CodeCopyer996/PProbot/3.Model/lianzhouqi.SLDPRT

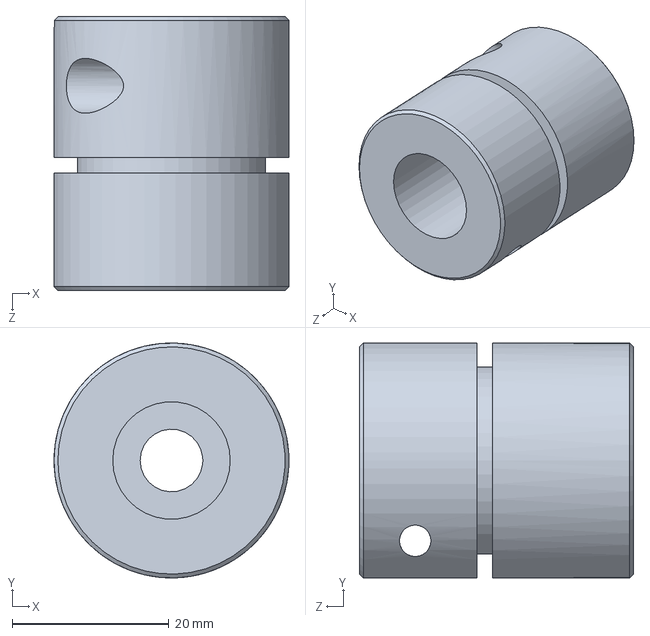
[picture p57: CAD file, 2023-08-03]
3.Model/lianzhouqi.SLDPRT
30.0 x 30.0 x 35.0 mm
