CodeCopyer996/PProbot/3.Model/大臂电机支架.SLDPRT

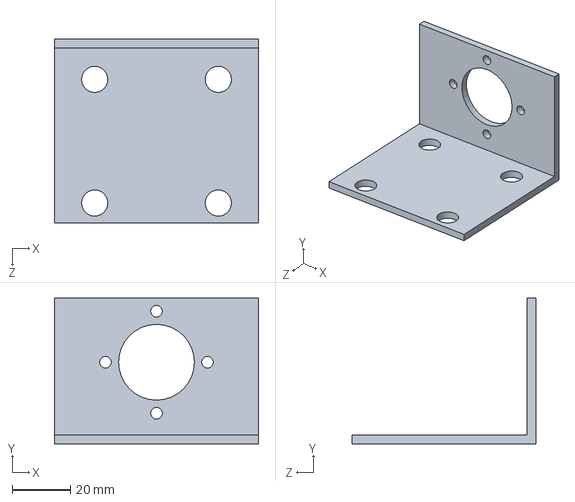
[picture p58: CAD file, 2023-08-03]
3.Model/大臂电机支架.SLDPRT
70.0 x 50.0 x 63.0 mm
