CodeCopyer996/PProbot/3.Model/6902带挡边轴承.SLDPRT

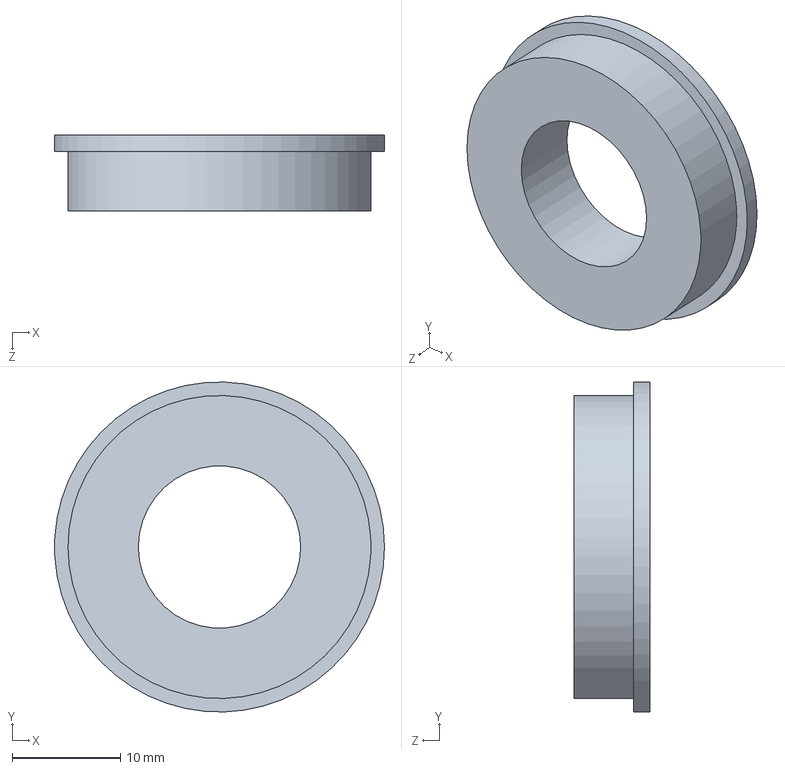
[picture p59: CAD file, 2023-08-03]
3.Model/6902带挡边轴承.SLDPRT
30.5 x 30.5 x 7.00 mm
