CodeCopyer996/PProbot/3.Model/27：1双轴减速器.SLDPRT

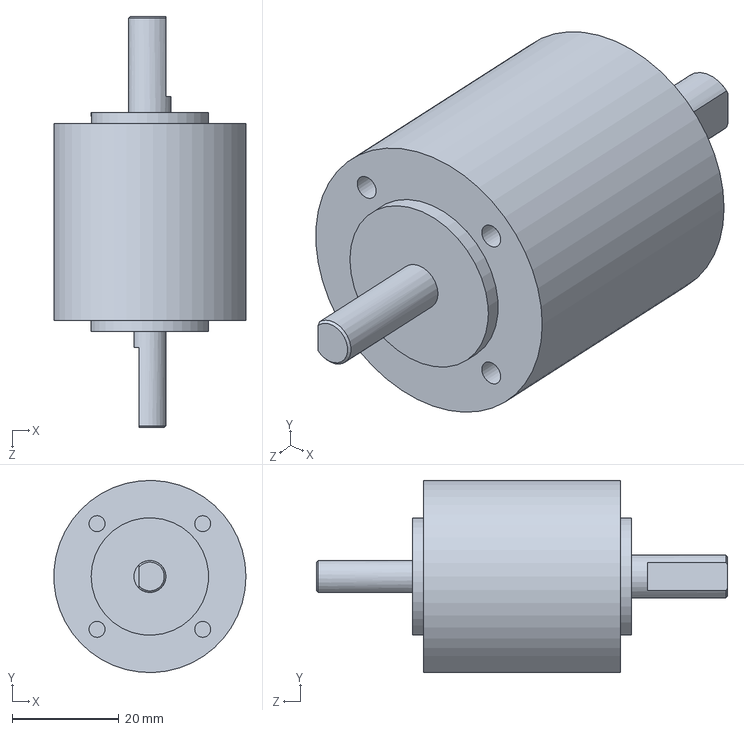
[picture p60: CAD file, 2023-08-03]
3.Model/27：1双轴减速器.SLDPRT
36.0 x 36.0 x 77.0 mm
