CodeCopyer996/PProbot/3.Model/小臂右1.SLDPRT

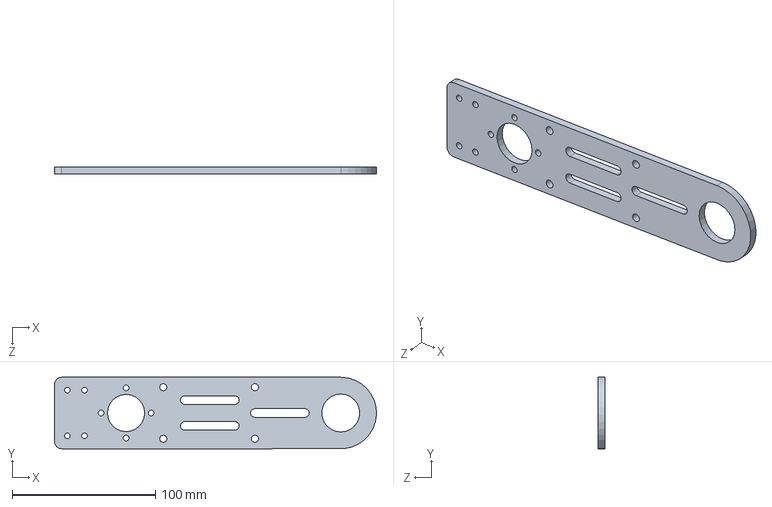
[picture p61: CAD file, 2023-08-03]
3.Model/小臂右1.SLDPRT
225.0 x 50.0 x 5.00 mm
