CodeCopyer996/PProbot/3.Model/皮带10-11.SLDPRT

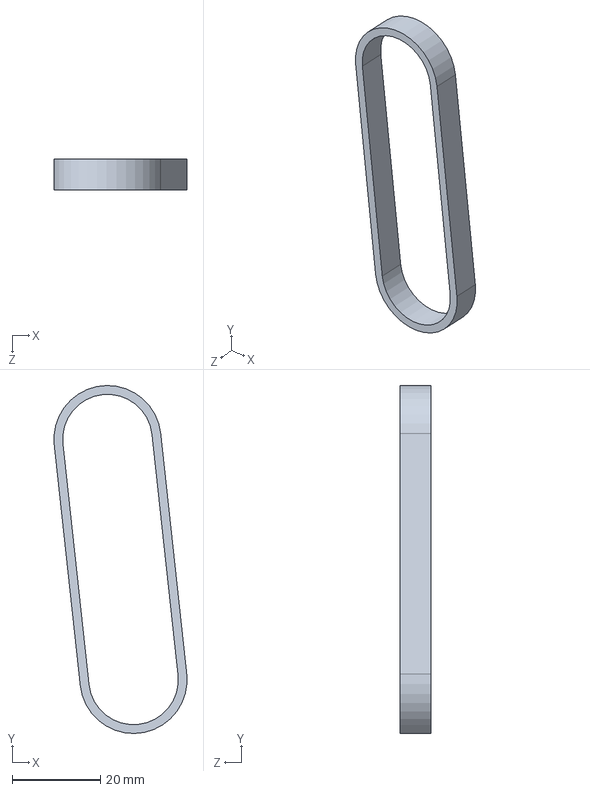
[picture p62: CAD file, 2023-08-03]
3.Model/皮带10-11.SLDPRT
30.1 x 78.8 x 7.00 mm
