CodeCopyer996/PProbot/3.Model/减速器固定.SLDPRT

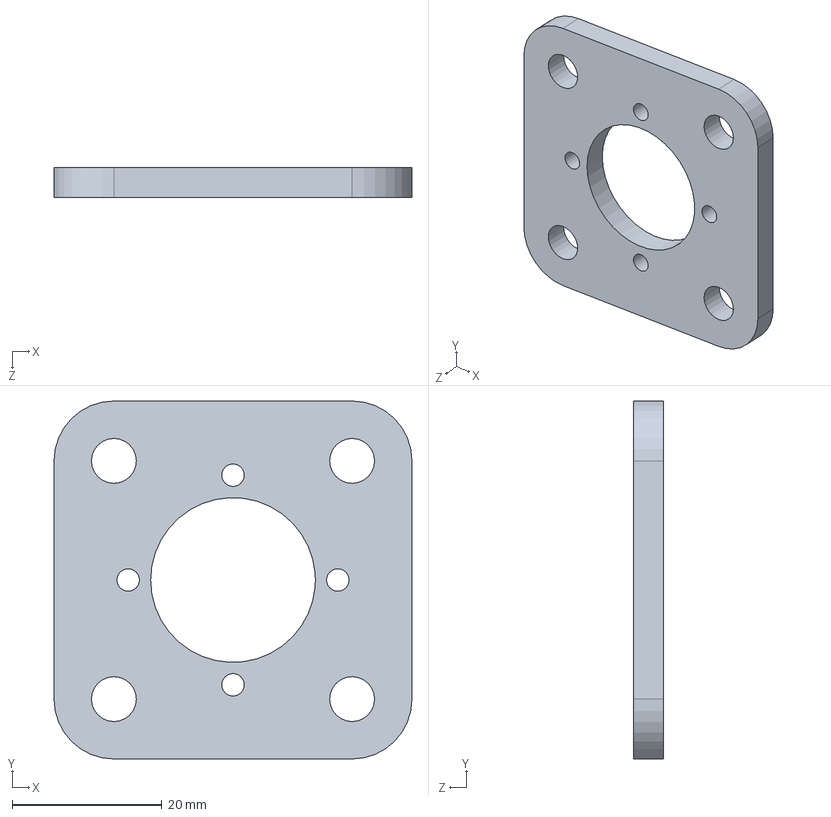
[picture p63: CAD file, 2023-08-03]
3.Model/减速器固定.SLDPRT
47.8 x 47.8 x 4.00 mm
