CodeCopyer996/PProbot/3.Model/小臂中.SLDPRT

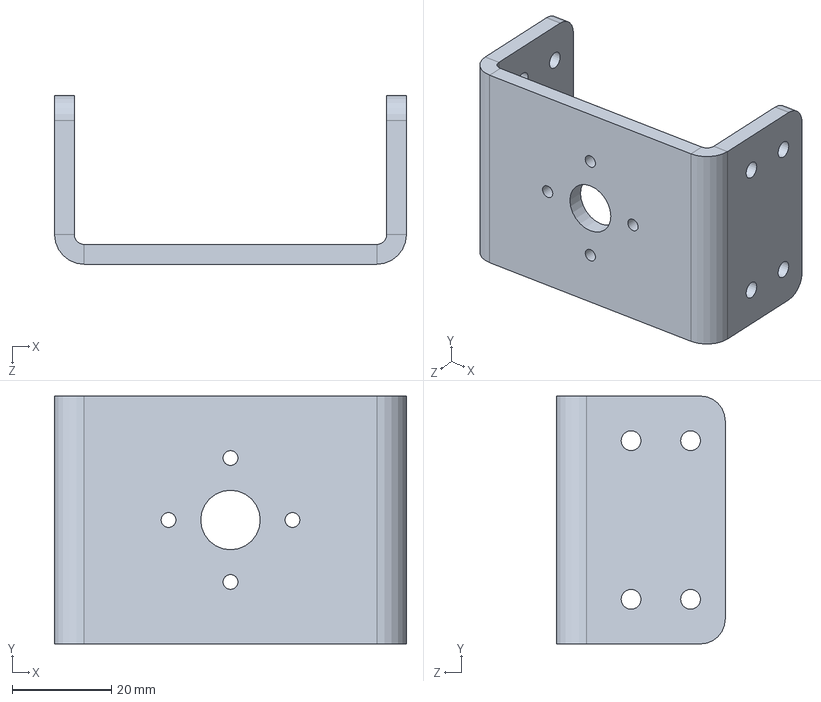
[picture p64: CAD file, 2023-08-03]
3.Model/小臂中.SLDPRT
71.0 x 50.0 x 34.0 mm
