CodeCopyer996/PProbot/3.Model/旋转轴6.SLDPRT

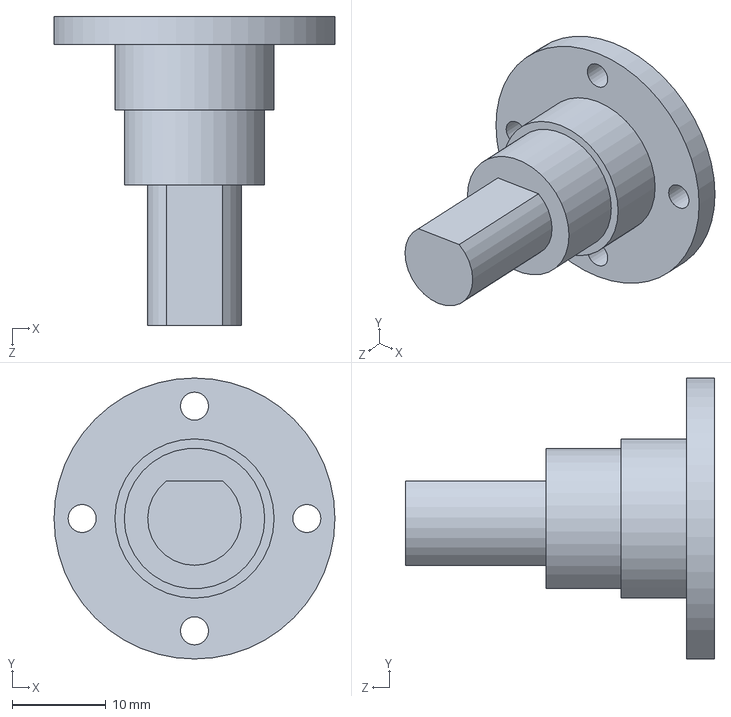
[picture p65: CAD file, 2023-08-03]
3.Model/旋转轴6.SLDPRT
30.0 x 30.0 x 33.0 mm
