CodeCopyer996/PProbot/3.Model/底座支撑.SLDPRT

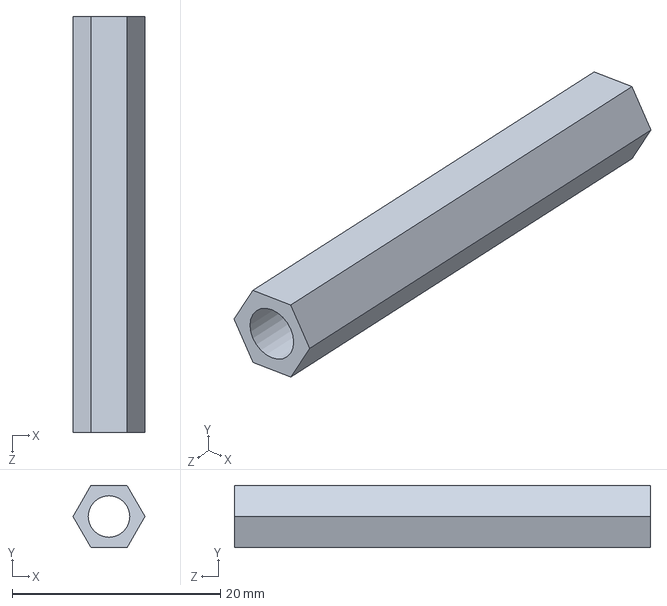
[picture p66: CAD file, 2023-08-03]
3.Model/底座支撑.SLDPRT
6.93 x 6.01 x 40.0 mm
