CodeCopyer996/PProbot/3.Model/大臂.SLDPRT

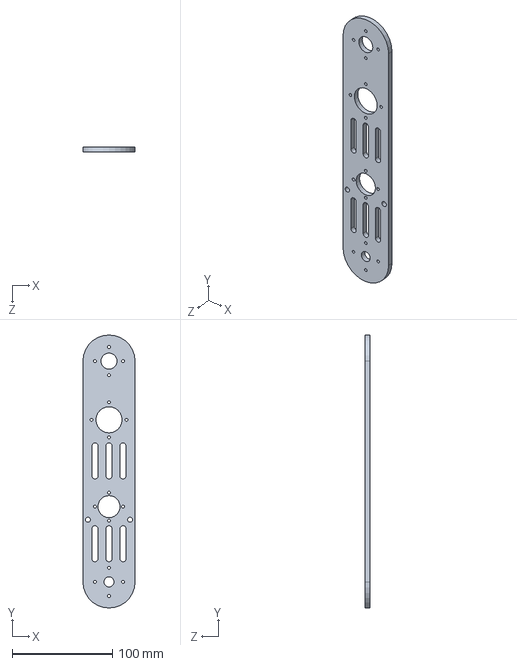
[picture p67: CAD file, 2023-08-03]
3.Model/大臂.SLDPRT
52.0 x 272.0 x 5.00 mm
