CodeCopyer996/PProbot/3.Model/云台旋转板.SLDPRT

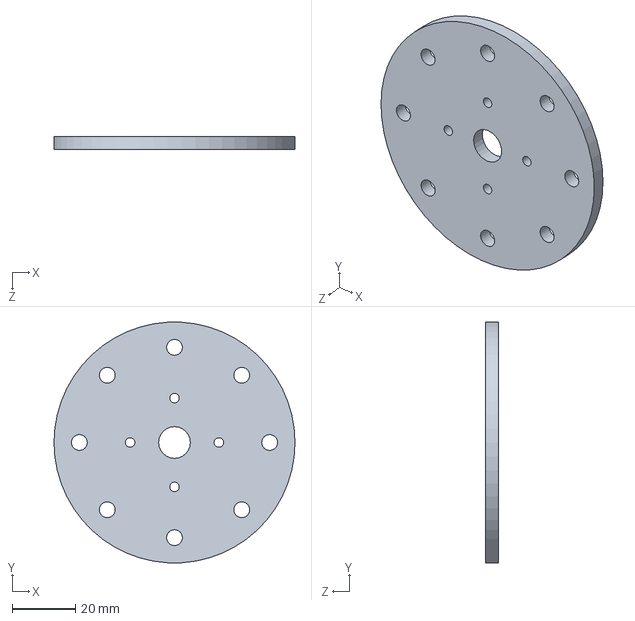
[picture p68: CAD file, 2023-08-03]
3.Model/云台旋转板.SLDPRT
76.0 x 75.9 x 4.00 mm
