CodeCopyer996/PProbot/3.Model/小臂p1.SLDPRT

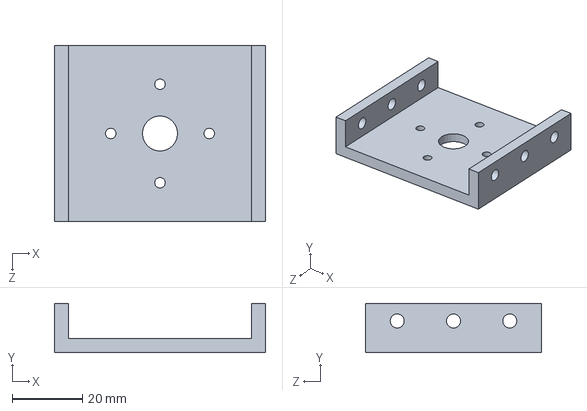
[picture p69: CAD file, 2023-08-03]
3.Model/小臂p1.SLDPRT
60.0 x 14.0 x 50.0 mm
