CodeCopyer996/PProbot/3.Model/小臂支架1.SLDPRT

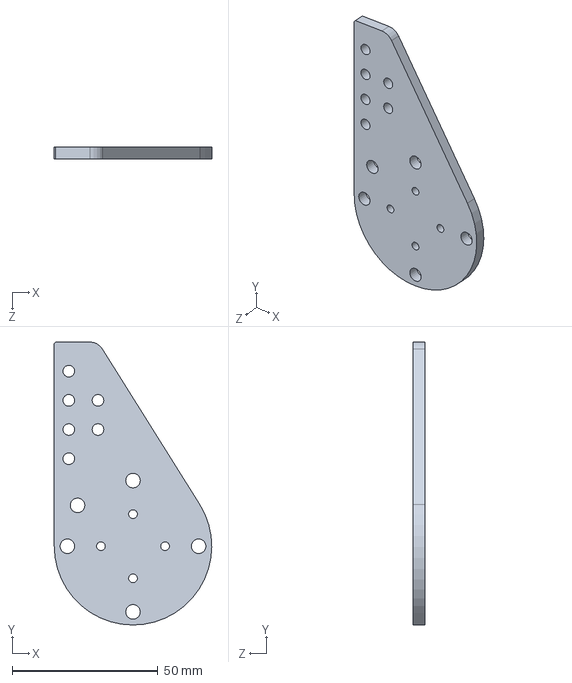
[picture p70: CAD file, 2023-08-03]
3.Model/小臂支架1.SLDPRT
54.0 x 97.0 x 4.00 mm
