CodeCopyer996/PProbot/3.Model/大臂支架左.SLDPRT

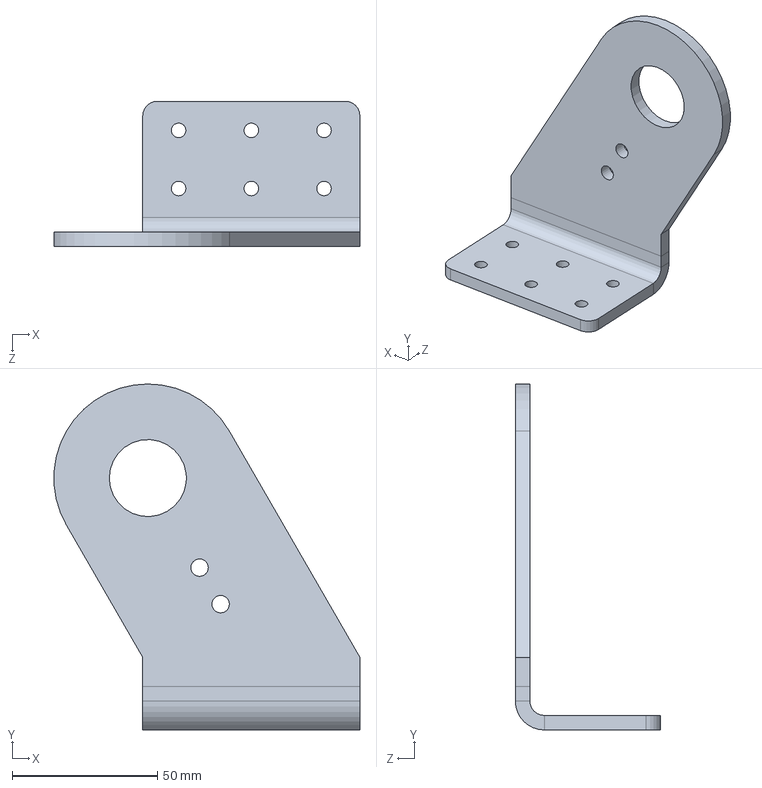
[picture p71: CAD file, 2023-08-03]
3.Model/大臂支架左.SLDPRT
105.2 x 119.0 x 50.0 mm
