CodeCopyer996/PProbot/3.Model/爪.SLDPRT

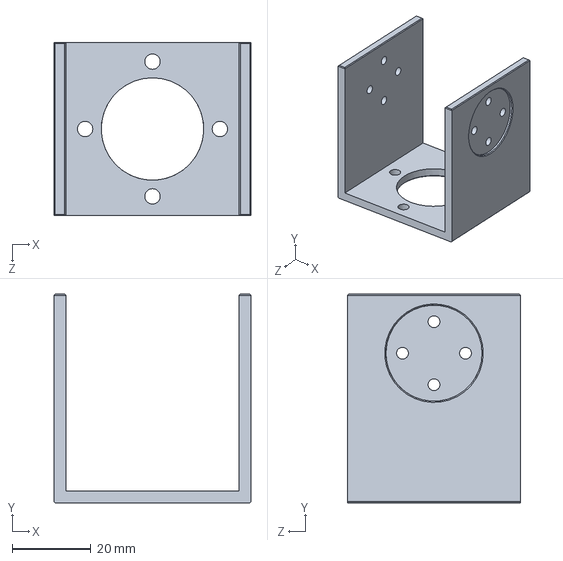
[picture p73: CAD file, 2023-08-03]
3.Model/爪.SLDPRT
50.0 x 53.0 x 44.0 mm
