CodeCopyer996/PProbot/3.Model/皮带4-5.SLDPRT

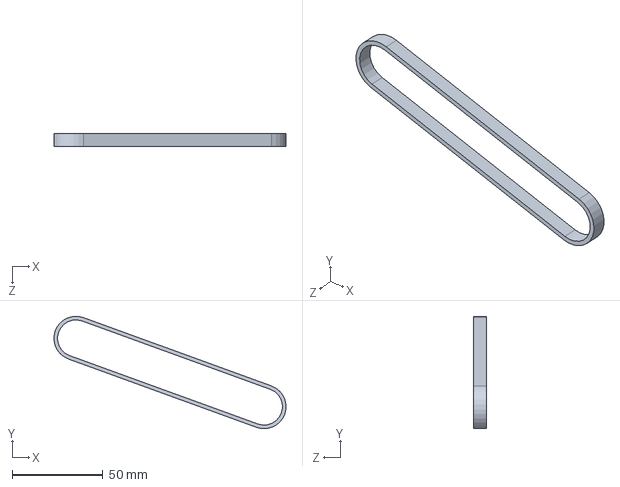
[picture p74: CAD file, 2023-08-03]
3.Model/皮带4-5.SLDPRT
127.7 x 61.7 x 7.00 mm
