CodeCopyer996/PProbot/3.Model/大臂支架.SLDPRT

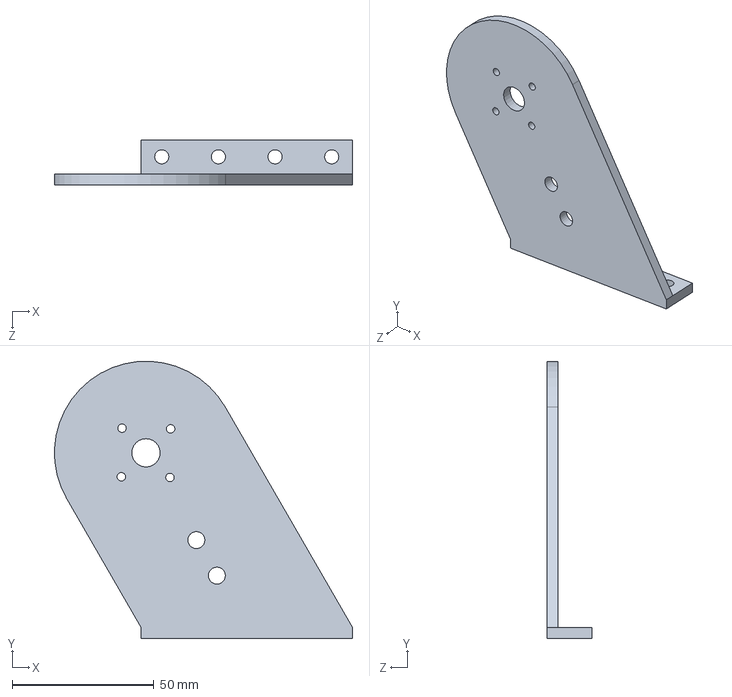
[picture p75: CAD file, 2023-08-03]
3.Model/大臂支架.SLDPRT
105.2 x 97.9 x 16.0 mm
