CodeCopyer996/PProbot/3.Model/皮带11-12.SLDPRT

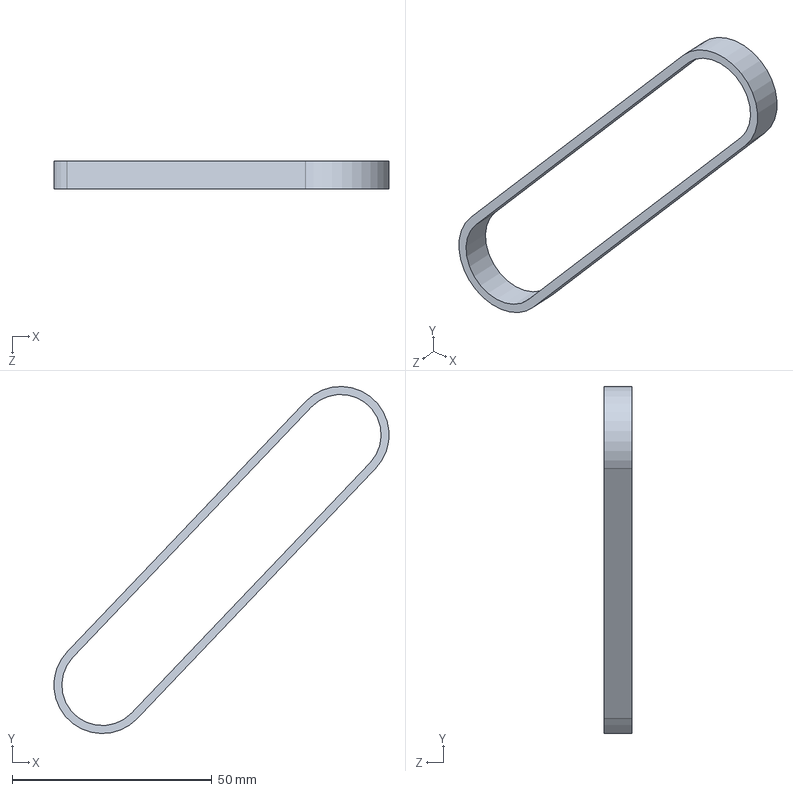
[picture p76: CAD file, 2023-08-03]
3.Model/皮带11-12.SLDPRT
83.8 x 86.9 x 7.00 mm
