CodeCopyer996/PProbot/3.Model/地板.SLDPRT

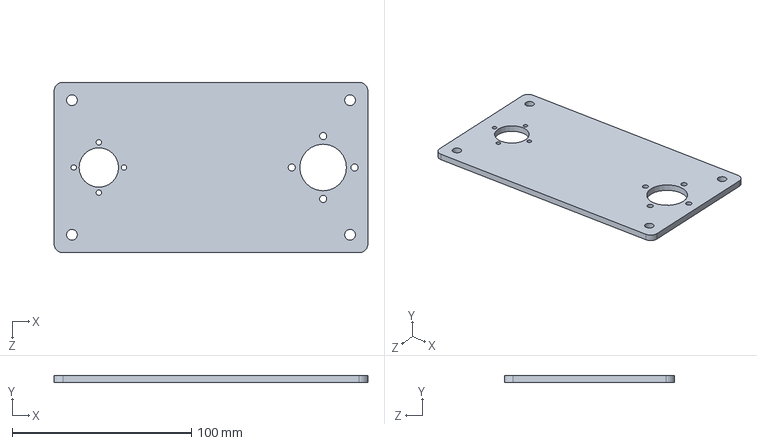
[picture p77: CAD file, 2023-08-03]
3.Model/地板.SLDPRT
175.0 x 4.00 x 95.0 mm
