CodeCopyer996/PProbot/3.Model/电机固定板.SLDPRT

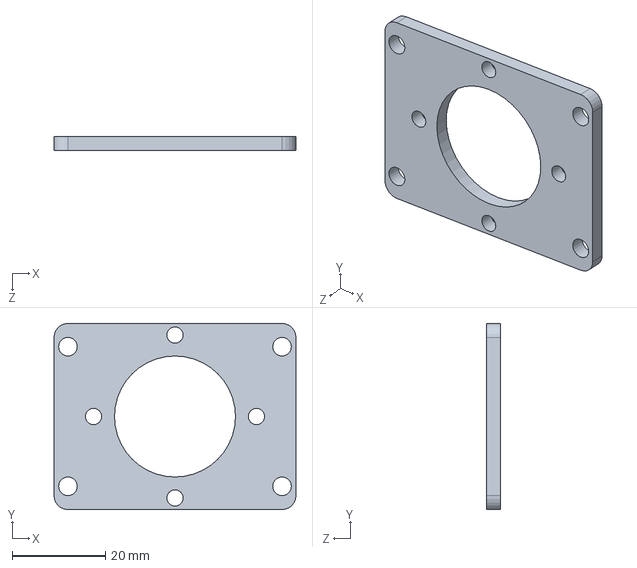
[picture p78: CAD file, 2023-08-03]
3.Model/电机固定板.SLDPRT
52.0 x 40.0 x 3.00 mm
