CodeCopyer996/PProbot/3.Model/小臂2支架.SLDPRT

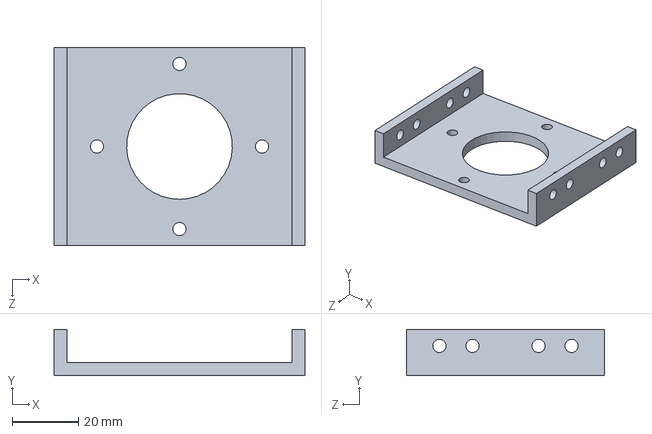
[picture p79: CAD file, 2023-08-03]
3.Model/小臂2支架.SLDPRT
76.0 x 14.0 x 60.0 mm
