CodeCopyer996/PProbot/3.Model/同步轮8.SLDPRT

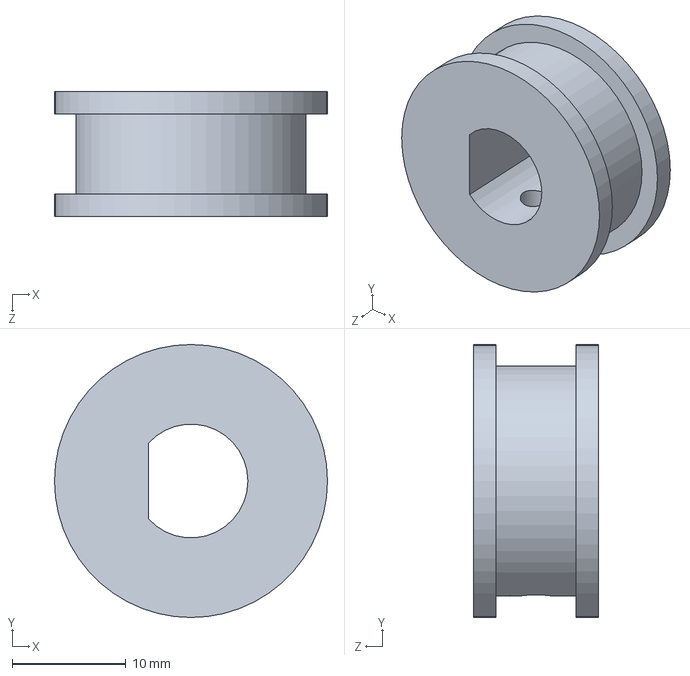
[picture p80: CAD file, 2023-08-03]
3.Model/同步轮8.SLDPRT
24.0 x 24.0 x 11.0 mm
