CodeCopyer996/PProbot/3.Model/云台法兰.SLDPRT

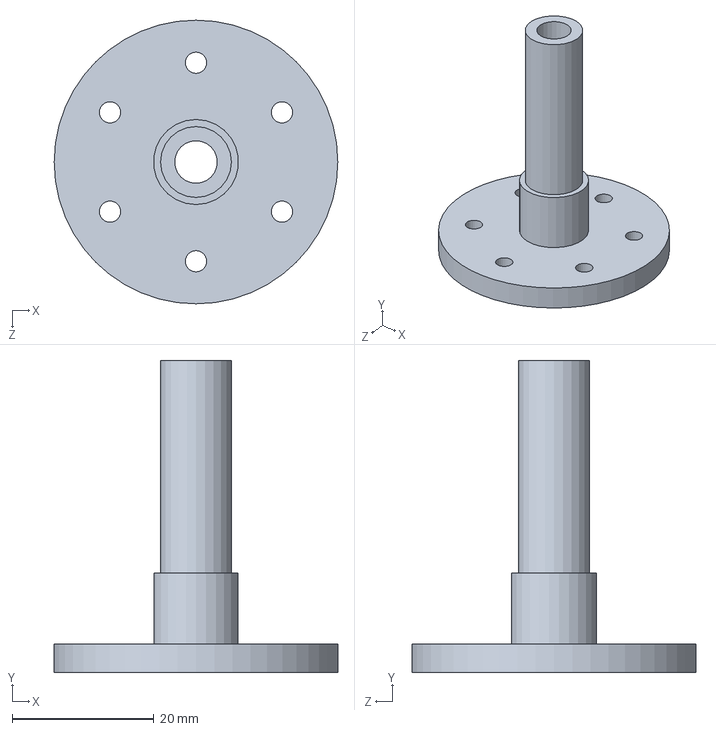
[picture p81: CAD file, 2023-08-03]
3.Model/云台法兰.SLDPRT
40.0 x 44.0 x 40.0 mm
