CodeCopyer996/PProbot/3.Model/小臂轴.SLDPRT

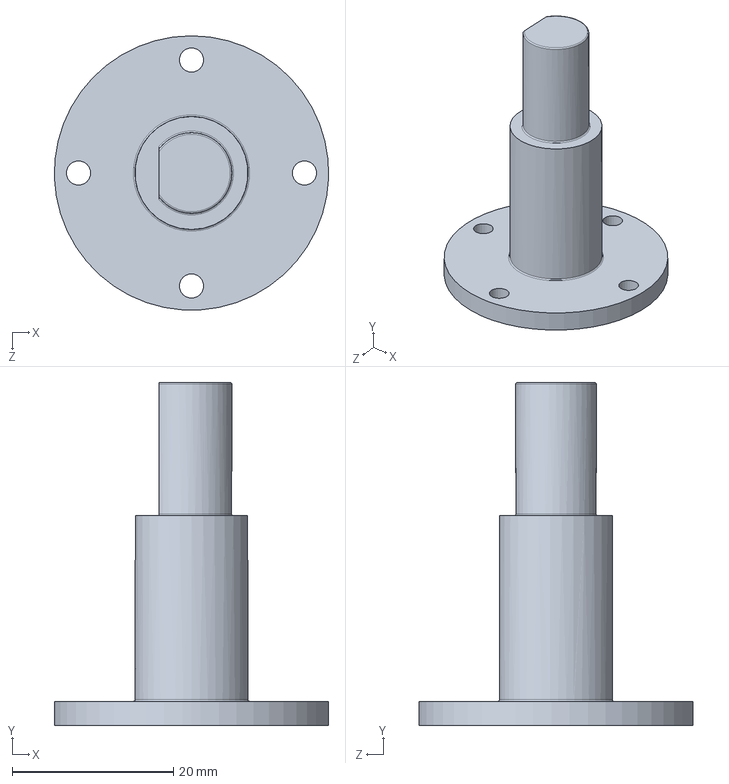
[picture p82: CAD file, 2023-08-03]
3.Model/小臂轴.SLDPRT
34.0 x 42.5 x 34.0 mm
