CodeCopyer996/PProbot/3.Model/云台法兰2.SLDPRT

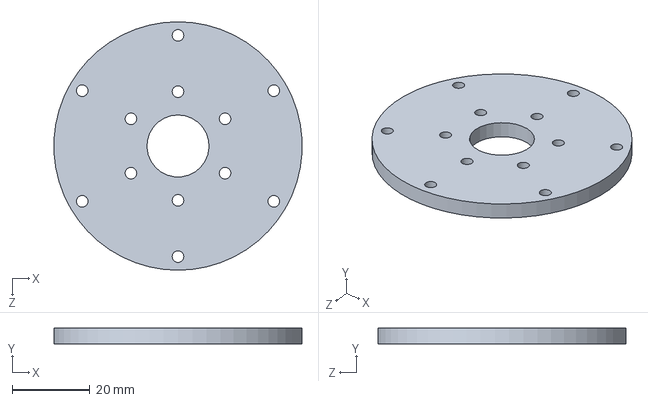
[picture p83: CAD file, 2023-08-03]
3.Model/云台法兰2.SLDPRT
63.9 x 4.00 x 64.0 mm
