CodeCopyer996/PProbot/3.Model/小臂中支架2.SLDPRT

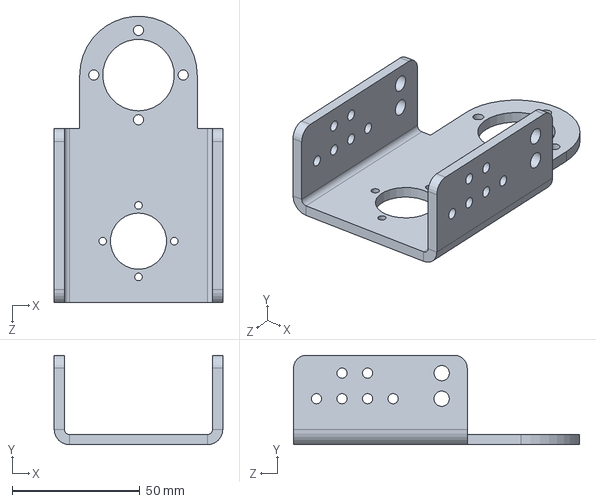
[picture p84: CAD file, 2023-08-03]
3.Model/小臂中支架2.SLDPRT
66.0 x 35.0 x 111.9 mm
