CodeCopyer996/PProbot/3.Model/皮带9-10.SLDPRT

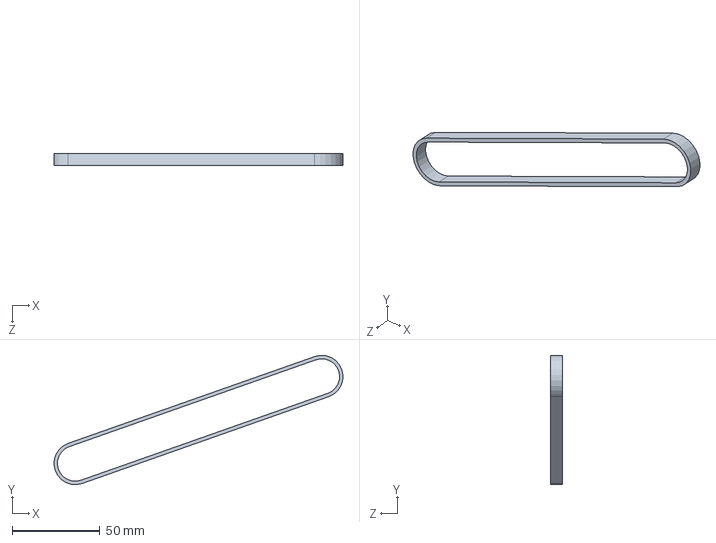
[picture p85: CAD file, 2023-08-03]
3.Model/皮带9-10.SLDPRT
164.8 x 73.7 x 7.00 mm
