CodeCopyer996/PProbot/3.Model/71铜柱.SLDPRT

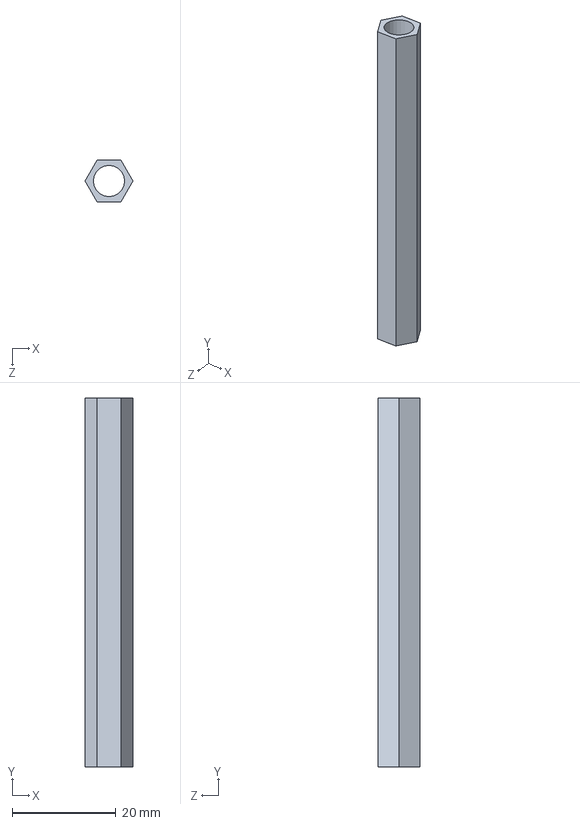
[picture p86: CAD file, 2023-08-03]
3.Model/71铜柱.SLDPRT
9.24 x 71.0 x 8.00 mm
