CodeCopyer996/PProbot/3.Model/铜柱M6x6.SLDPRT

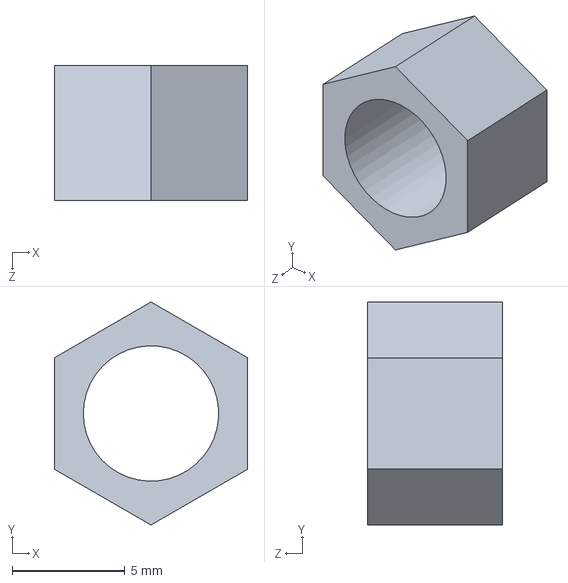
[picture p87: CAD file, 2023-08-03]
3.Model/铜柱M6x6.SLDPRT
8.56 x 9.88 x 6.00 mm
