CodeCopyer996/PProbot/3.Model/云台法兰42.SLDPRT

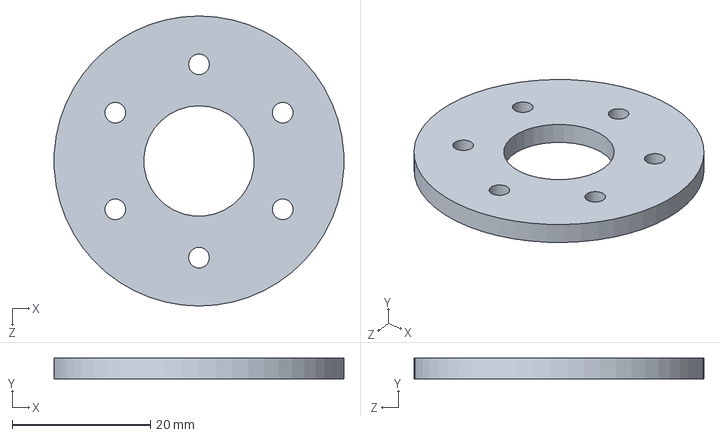
[picture p88: CAD file, 2023-08-03]
3.Model/云台法兰42.SLDPRT
41.9 x 3.00 x 42.0 mm
