CodeCopyer996/PProbot/3.Model/底板F1.SLDPRT

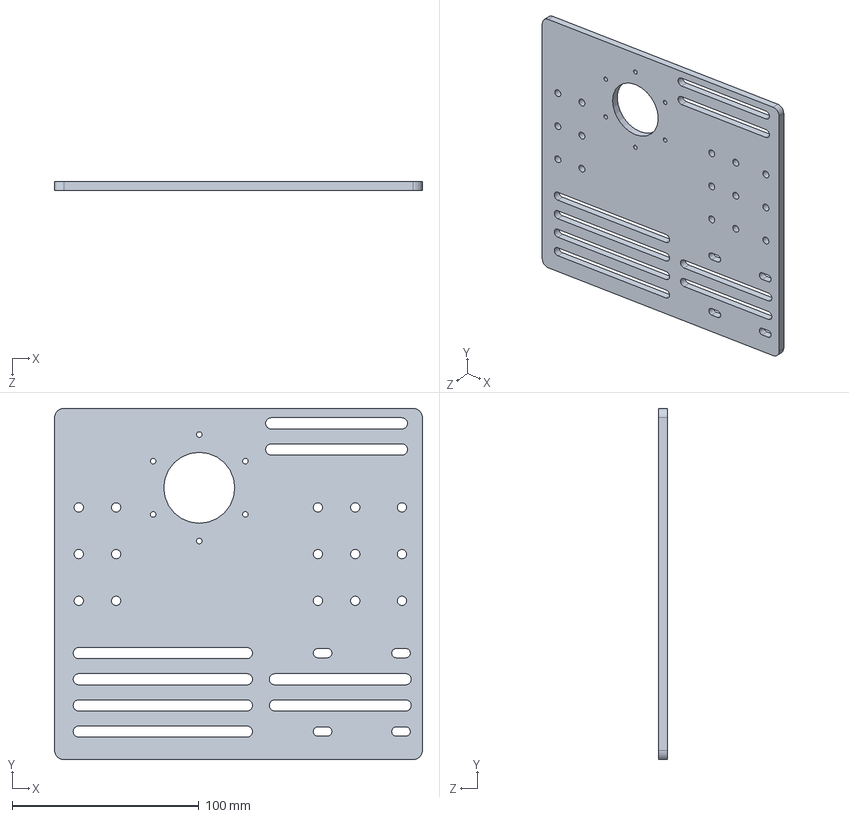
[picture p89: CAD file, 2023-08-03]
3.Model/底板F1.SLDPRT
197.0 x 188.0 x 5.00 mm
