CodeCopyer996/PProbot/3.Model/58铜柱.SLDPRT

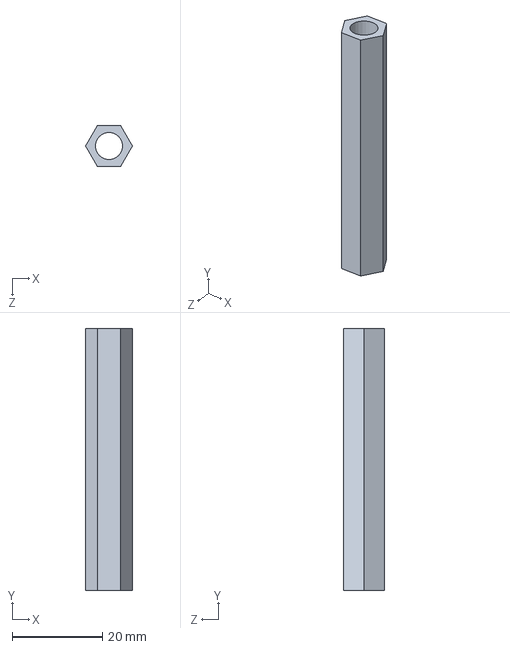
[picture p90: CAD file, 2023-08-03]
3.Model/58铜柱.SLDPRT
10.4 x 58.0 x 9.00 mm
