CodeCopyer996/PProbot/3.Model/小臂的2支架.SLDPRT

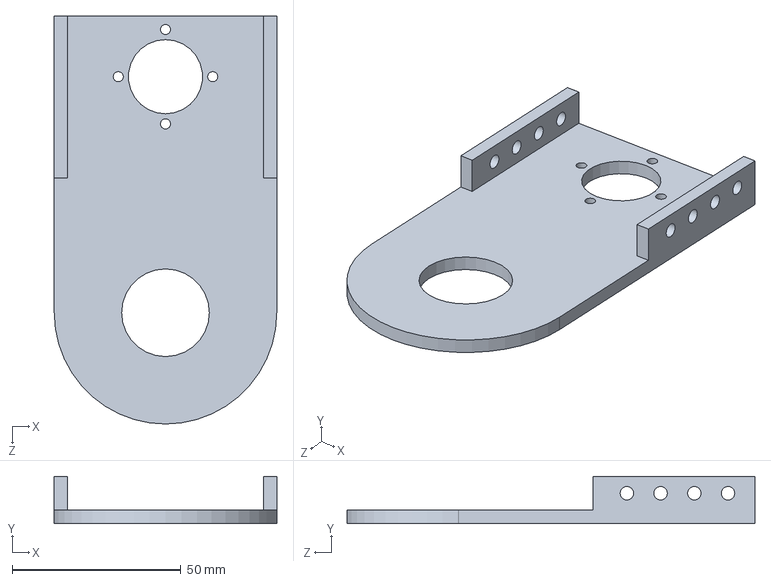
[picture p91: CAD file, 2023-08-03]
3.Model/小臂的2支架.SLDPRT
66.0 x 14.0 x 121.0 mm
