CodeCopyer996/PProbot/3.Model/云台联轴器8-10.SLDPRT

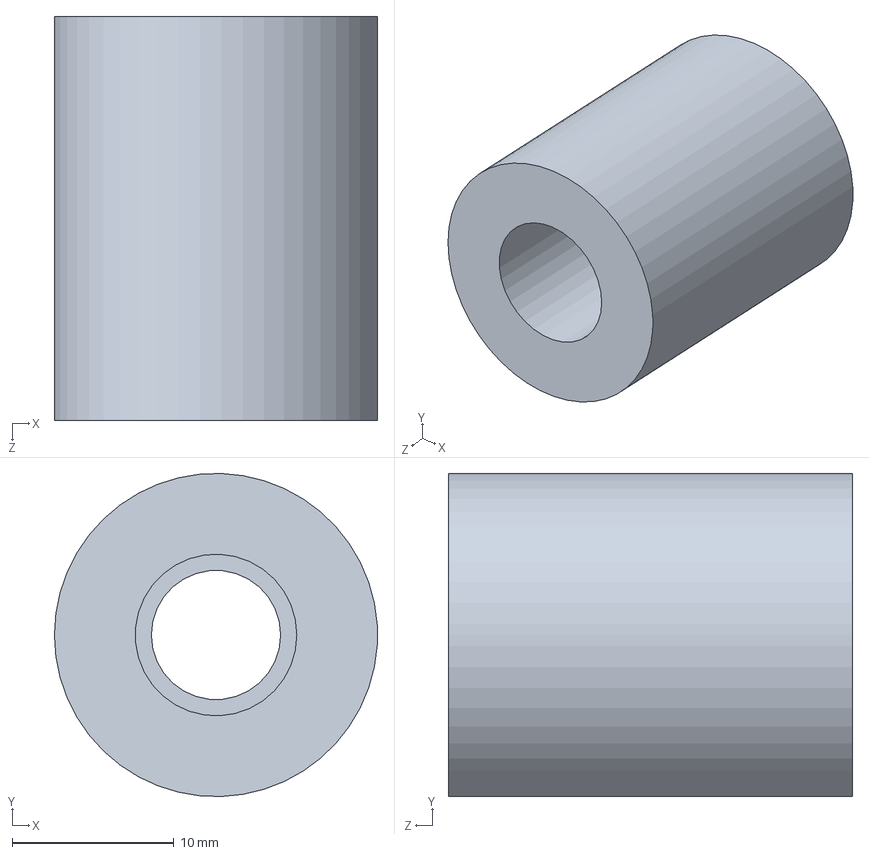
[picture p92: CAD file, 2023-08-03]
3.Model/云台联轴器8-10.SLDPRT
20.0 x 20.0 x 25.0 mm
