CodeCopyer996/PProbot/3.Model/小臂支架左.SLDPRT

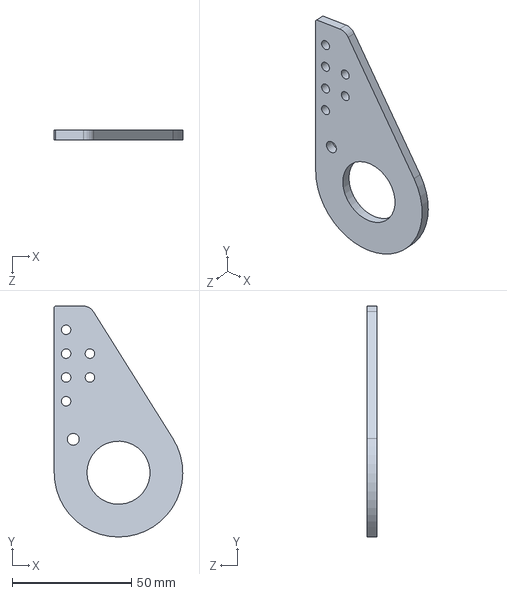
[picture p93: CAD file, 2023-08-03]
3.Model/小臂支架左.SLDPRT
54.0 x 97.0 x 4.00 mm
