CodeCopyer996/PProbot/3.Model/电机支柱.SLDPRT

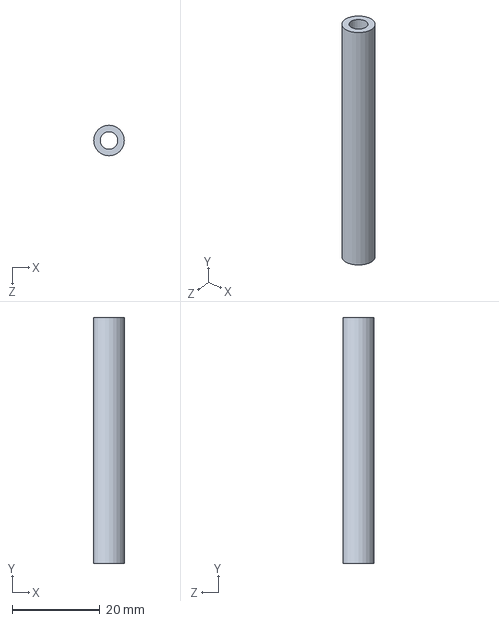
[picture p94: CAD file, 2023-08-03]
3.Model/电机支柱.SLDPRT
7.00 x 56.2 x 7.00 mm
