CodeCopyer996/PProbot/3.Model/皮带12-13.SLDPRT

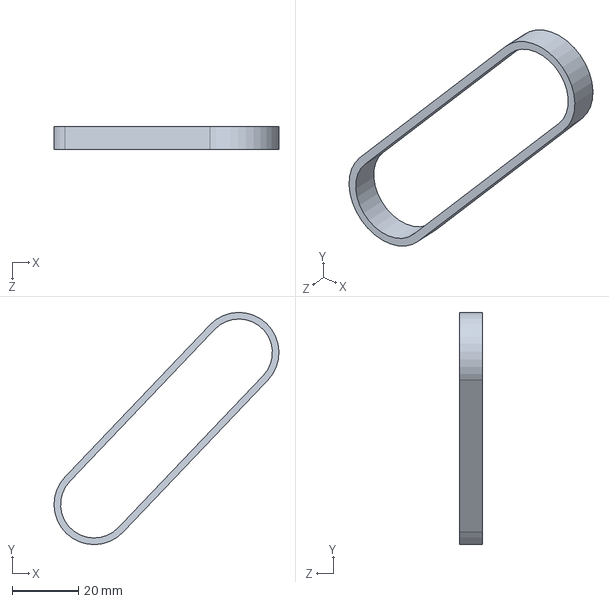
[picture p95: CAD file, 2023-08-03]
3.Model/皮带12-13.SLDPRT
68.0 x 70.2 x 7.00 mm
