CodeCopyer996/PProbot/2.ctrl_system/Controlsystem_v0.1/MyFreeRtos/Include/Basic_Task/base_calculation.h

#ifndef _BASE_CALCULATION_H_
#define _BASE_CALCULATION_H_

#include <Commnication_Task/CANCom.h>

#define PI	3.1415f

//角度格式化为弧度制
#define rad_format(ang)		loop_fp32_constrain(ang, -PI, PI)

//滤波器参数结构体
typedef struct{
	fp32 inout;				//输入数据
	fp32 out;				//滤波输出数据
	fp32 time_constant;		//滤波时间常数参数
	fp32 frame_period;		//滤波间隔时间
}__packed first_order_filter_t;


fp32 Fast_inv_square(fp32 num);
void first_order_filter_init(first_order_filter_t *filter_t_init, fp32 frame_period, const fp32 time_const);

void first_order_filter_calculation(first_order_filter_t *filter_t_cali, fp32 input);

fp32 fp32_constrain(fp32 value, fp32 min_value, fp32 max_value);	//限幅函数


#endif
