CodeCopyer996/PProbot/2.ctrl_system/Controlsystem_v0.1/MyFreeRtos/Include/Basic_Task/bsp_spi_dma.h

#ifndef __BSP_SPI_DMA_H__
#define __BSP_SPI_DMA_H__

#include "spi.h"
/*

#define SPI_DMA_GYRO_ACCEL_TEMP_LENGHT		14		//陀螺仪、加速度计、温度值传输长度
#define SPI_DMA_MSG_LENGHT					6		//磁力计传输长度


#define IMU_DR_SHIFT		0
#define IMU_SPI_SHIFT		1
#define IMU_UPDATA_SHIFT	2


void spi_dma_init(uint32_t tx_buffer, uint32_t rx_buffer, uint16_t num);
void spi_dma_enable(uint32_t tx_buffer, uint32_t rx_buffer, uint16_t num);*/

#endif
