CodeCopyer996/PProbot/2.ctrl_system/Controlsystem_v0.1/MyFreeRtos/Include/Sensor_Task/MeasureTask.h

#ifndef _MEASURE_TASK_H__
#define _MEASURE_TASK_H__

#include <Basic_Task/base_task.h>
#include <Sensor_Task/PressureMeasure.h>
#include <Sensor_Task/UltrasonicMeasure.h>


typedef struct {




}SensorMeasureData;


void ultrasonicMeasure();



#endif
